tebl/C64-PlayOnTape/documentation/datasheets/805_connector.png

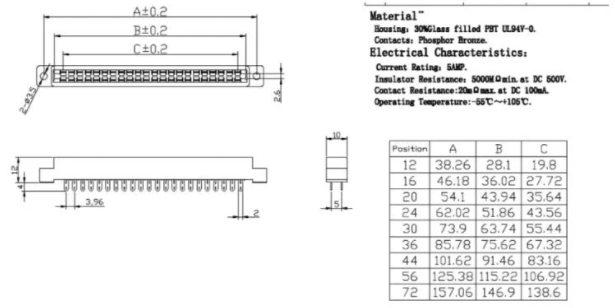
documentation/datasheets/805_connector.png
