tebl/C64-PlayOnTape/gallery/2022-02-19 01.37.31.jpg

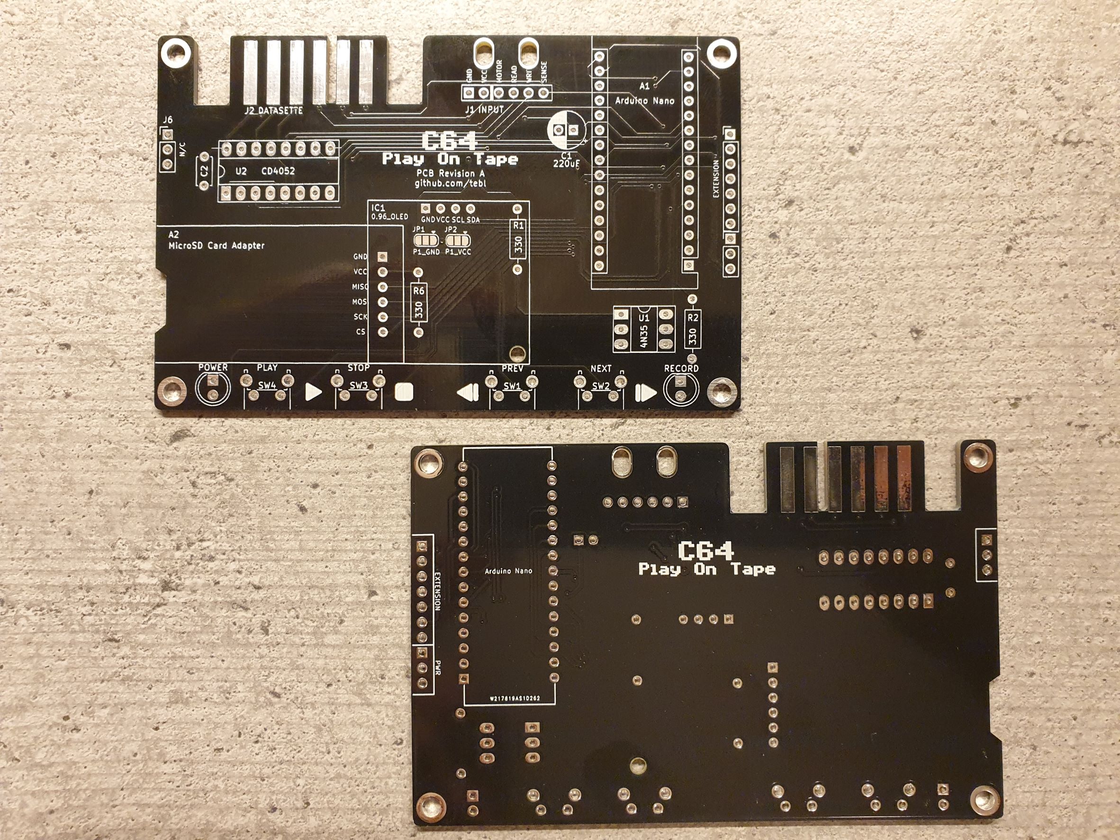
gallery/2022-02-19 01.37.31.jpg
