tebl/C64-PlayOnTape/gallery/2022-02-19 01.42.13.jpg

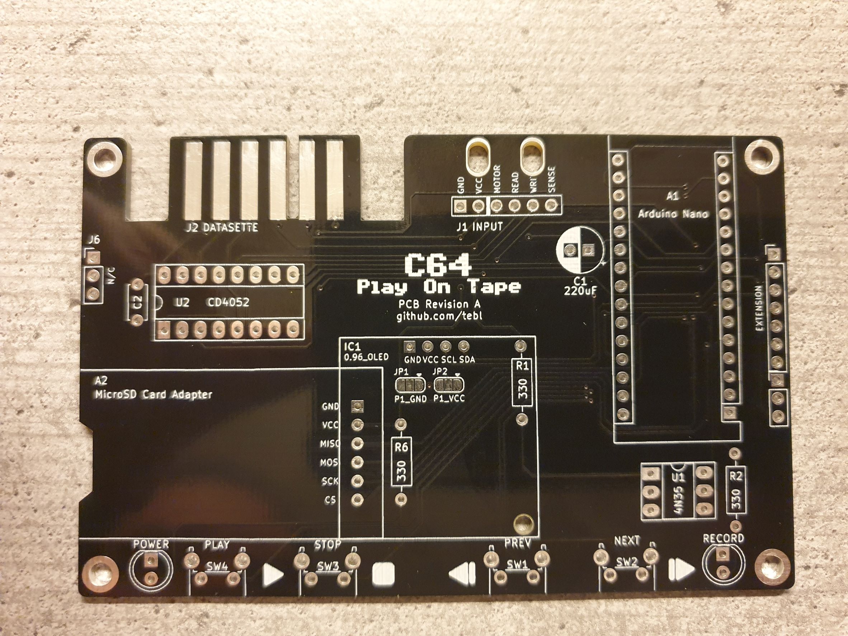
gallery/2022-02-19 01.42.13.jpg
