tebl/C64-PlayOnTape/gallery/2022-02-19 01.49.49.jpg

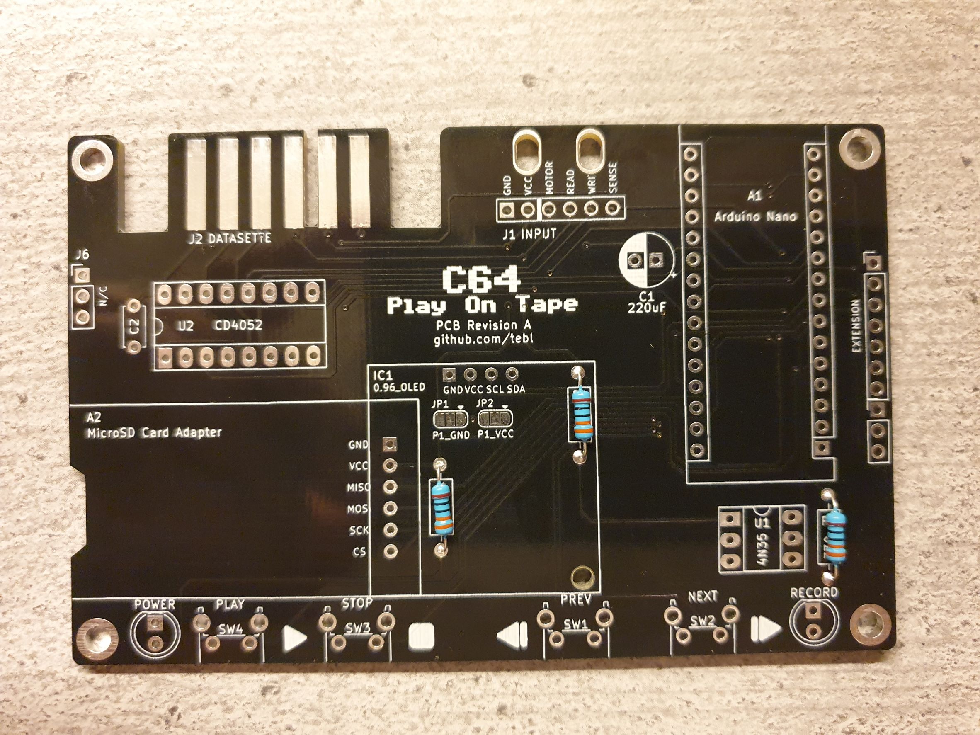
gallery/2022-02-19 01.49.49.jpg
