tebl/C64-PlayOnTape/gallery/2022-02-19 01.55.19.jpg

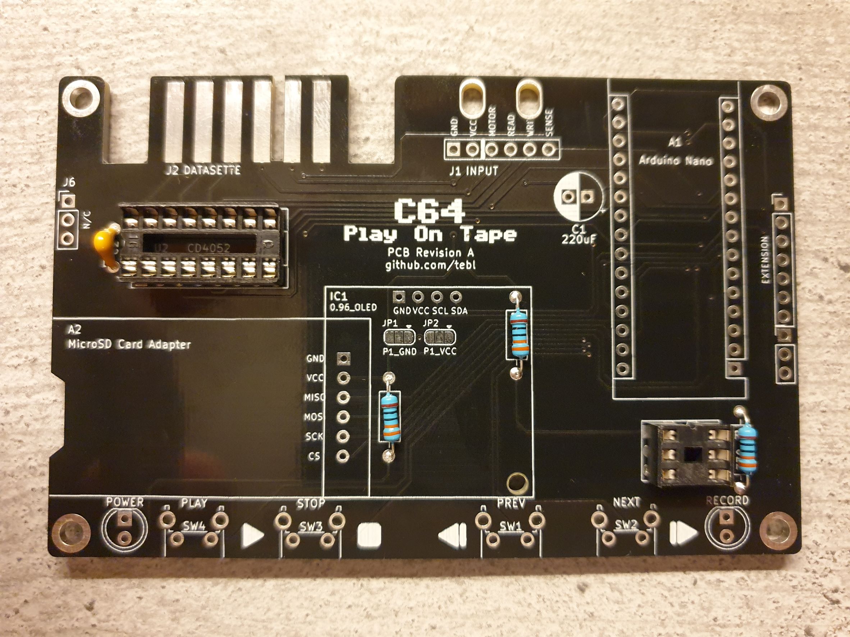
gallery/2022-02-19 01.55.19.jpg
