tebl/C64-PlayOnTape/gallery/2022-02-19 14.05.21.jpg

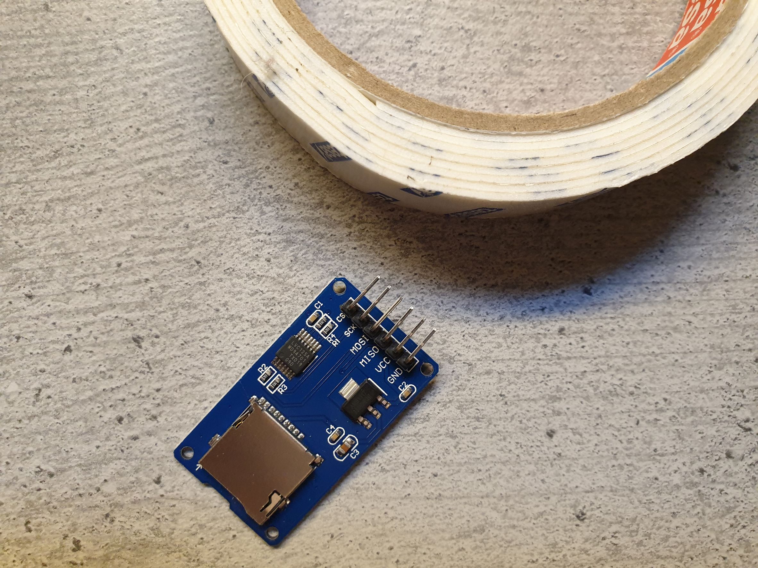
gallery/2022-02-19 14.05.21.jpg
