tebl/C64-PlayOnTape/gallery/2022-02-19 14.07.42.jpg

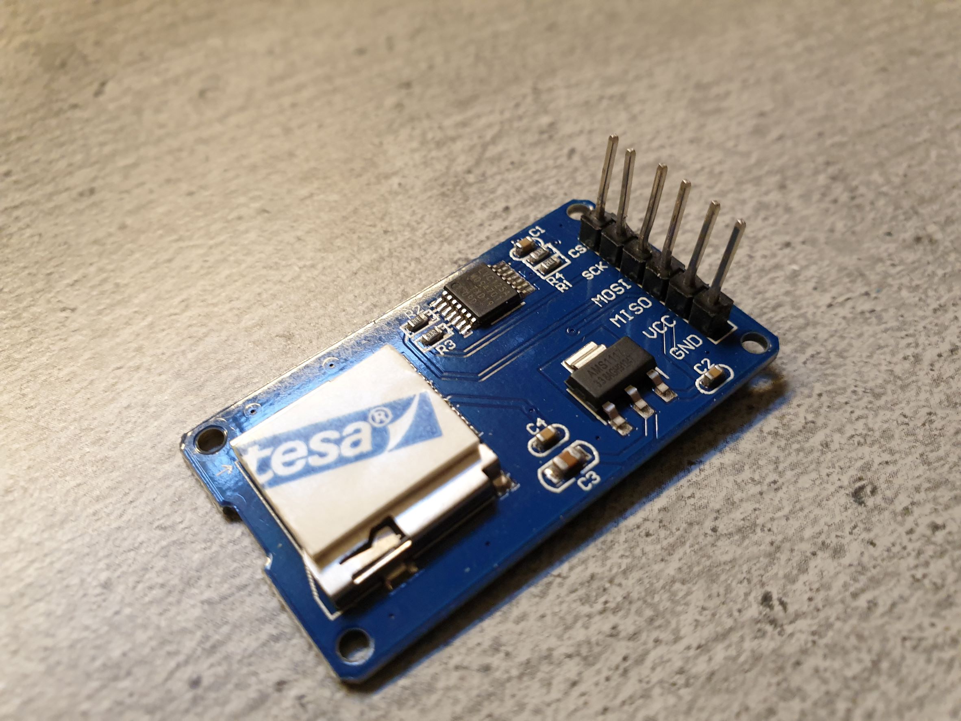
gallery/2022-02-19 14.07.42.jpg
