tebl/C64-PlayOnTape/gallery/2022-02-19 14.13.17.jpg

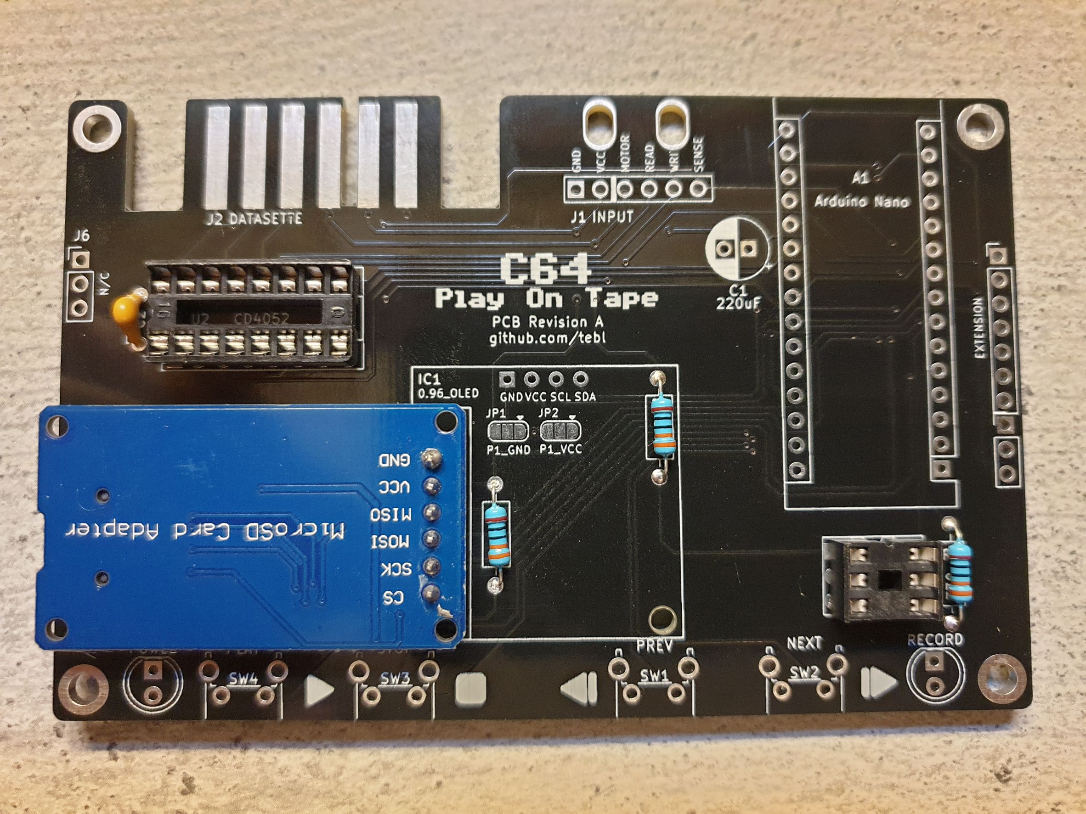
gallery/2022-02-19 14.13.17.jpg
