tebl/C64-PlayOnTape/gallery/2022-02-19 14.19.57.jpg

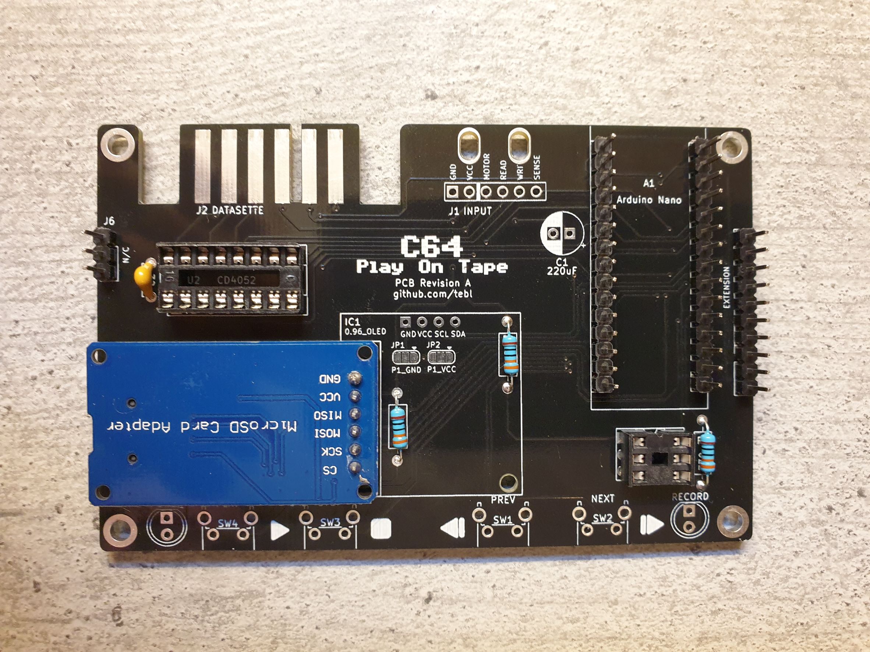
gallery/2022-02-19 14.19.57.jpg
