tebl/C64-PlayOnTape/gallery/2022-02-19 14.29.56.jpg

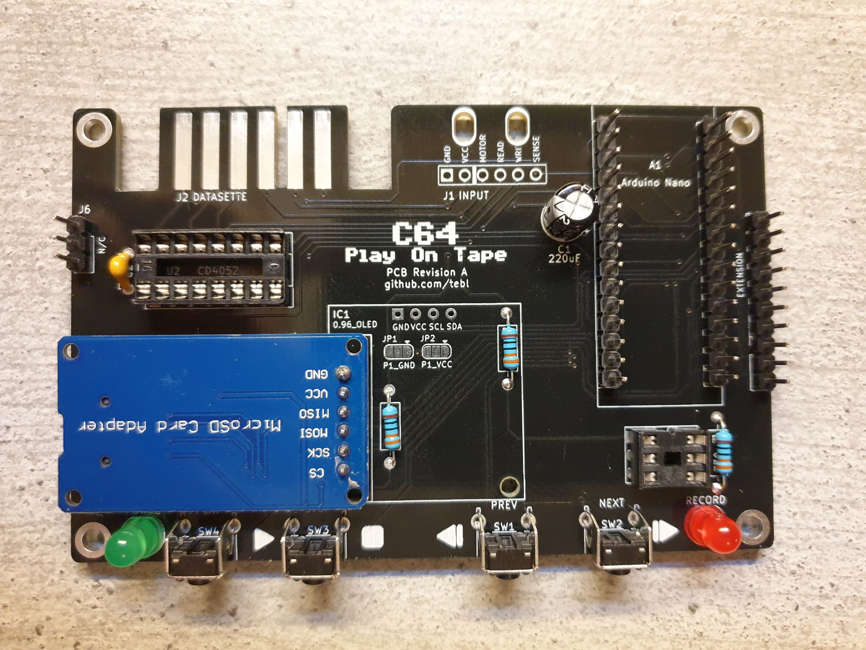
gallery/2022-02-19 14.29.56.jpg
