tebl/C64-PlayOnTape/gallery/2022-02-19 14.39.34.jpg

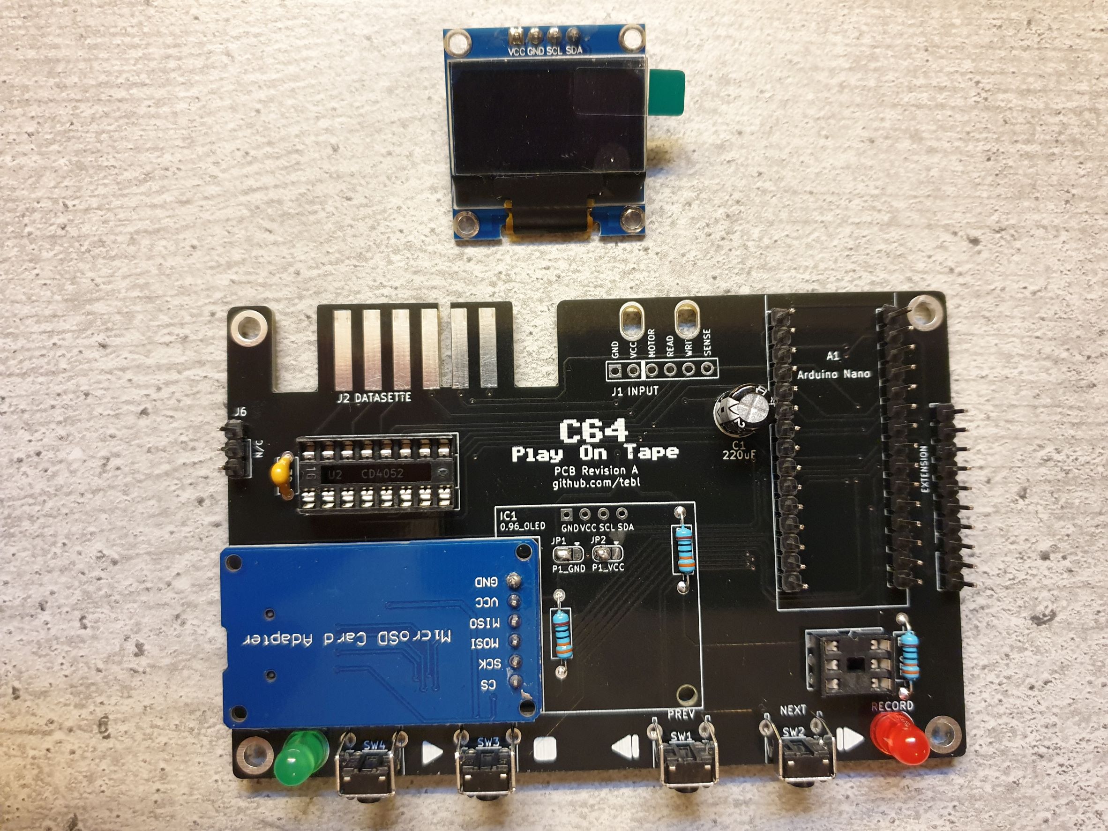
gallery/2022-02-19 14.39.34.jpg
