tebl/C64-PlayOnTape/gallery/2022-02-19 15.20.28.jpg

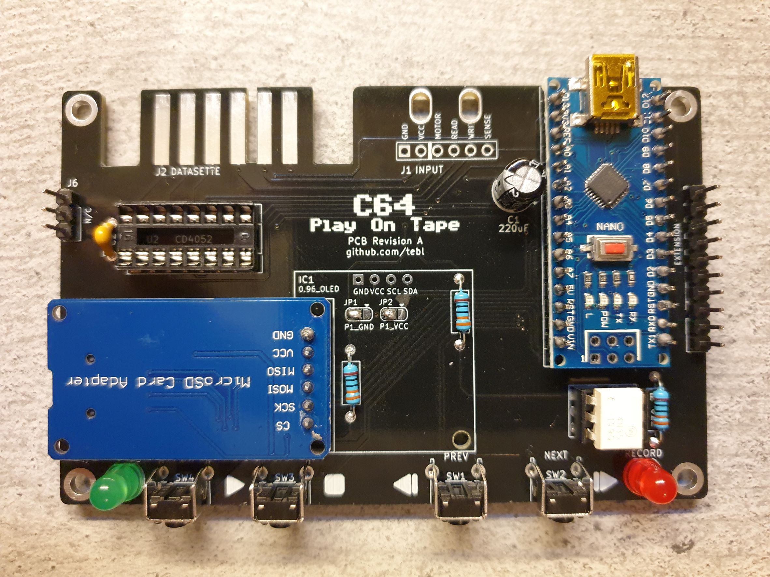
gallery/2022-02-19 15.20.28.jpg
