tebl/C64-PlayOnTape/gallery/2022-03-01 22.02.21.jpg

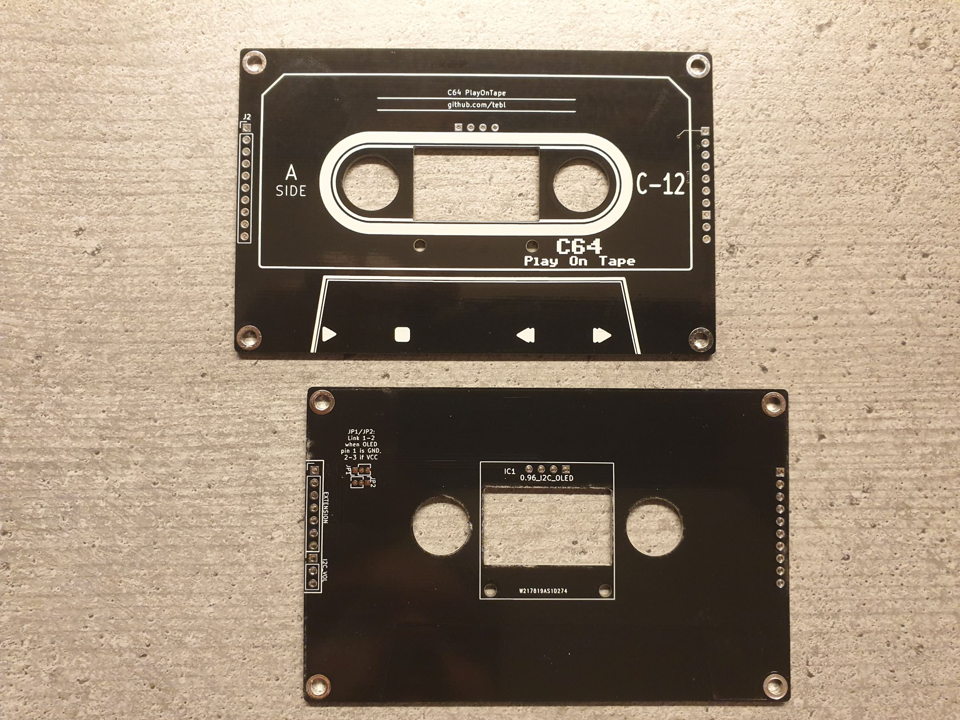
gallery/2022-03-01 22.02.21.jpg
