tebl/C64-PlayOnTape/gallery/2022-03-01 22.38.25.jpg

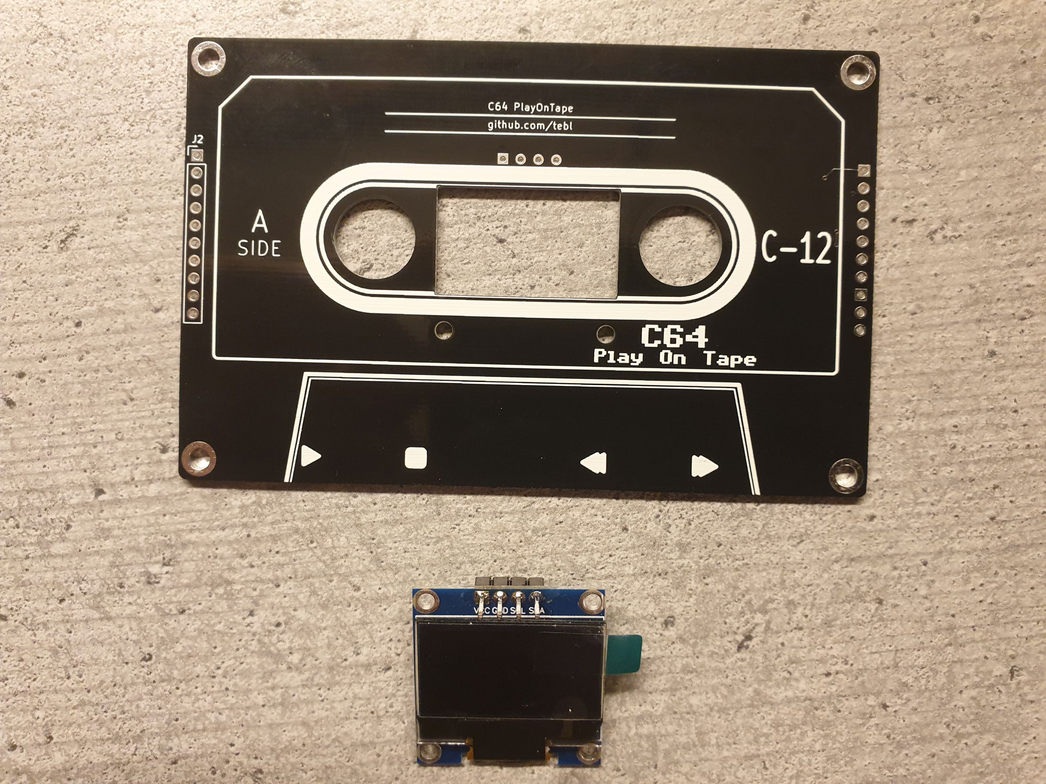
gallery/2022-03-01 22.38.25.jpg
