tebl/C64-PlayOnTape/gallery/2022-03-01 22.48.48.jpg

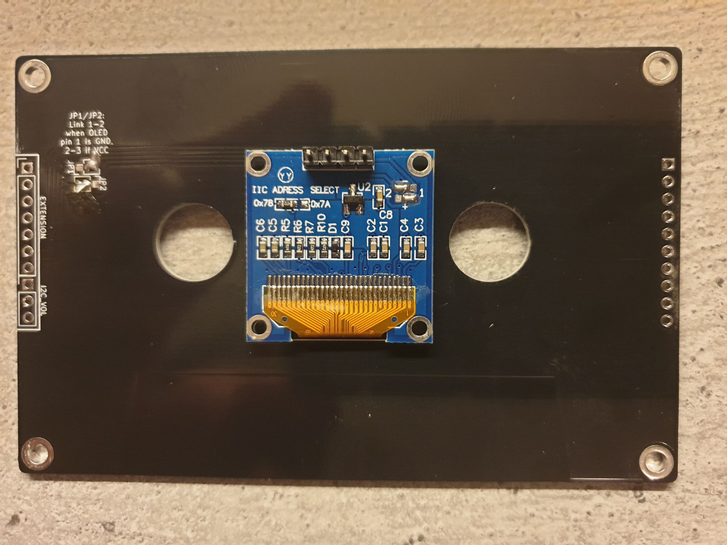
gallery/2022-03-01 22.48.48.jpg
