tebl/C64-PlayOnTape/gallery/2022-03-01 23.01.23.jpg

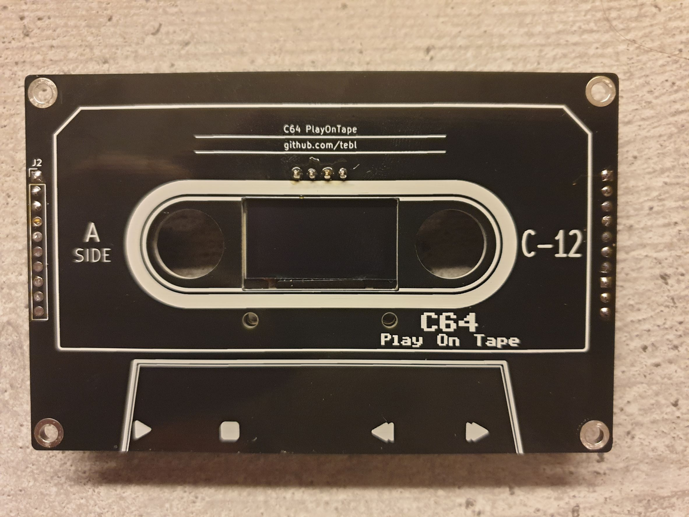
gallery/2022-03-01 23.01.23.jpg
