tebl/C64-PlayOnTape/gallery/2022-03-01 23.46.57.jpg

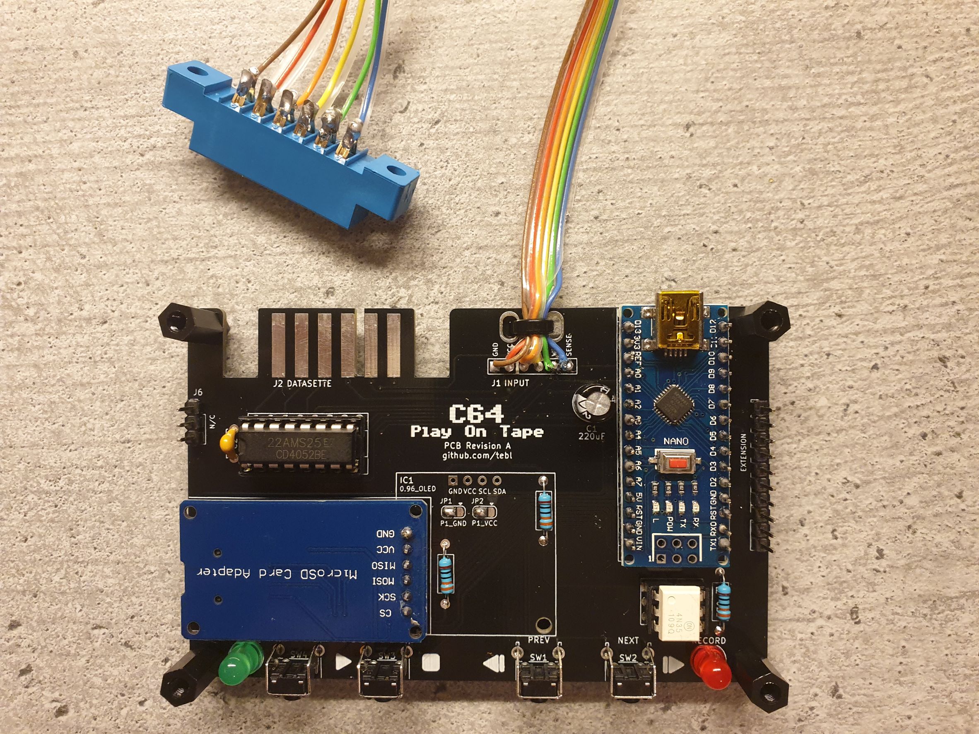
gallery/2022-03-01 23.46.57.jpg
