tebl/C64-PlayOnTape/gallery/2022-03-01 23.49.48.jpg

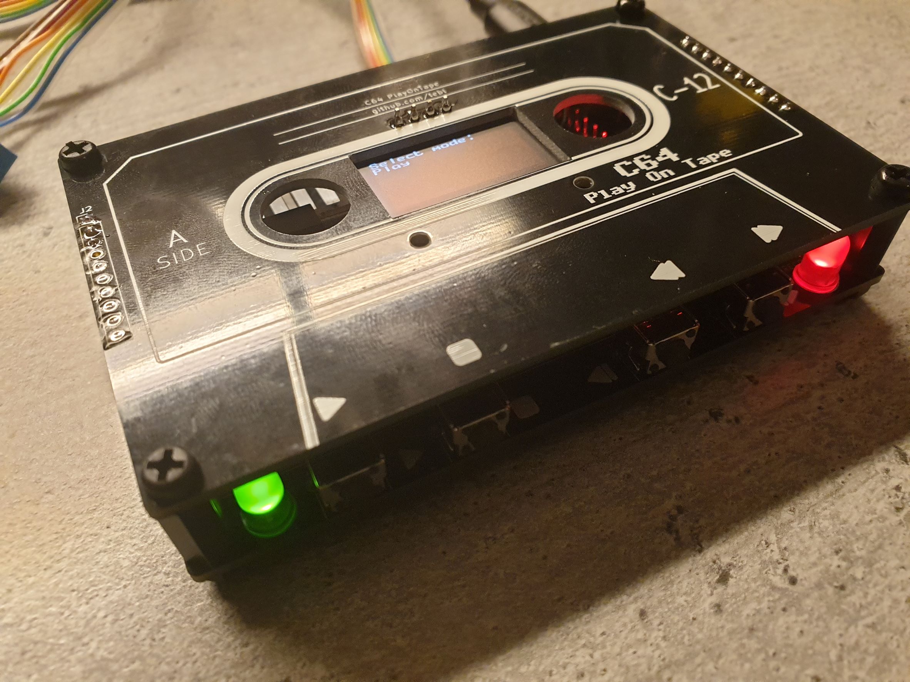
gallery/2022-03-01 23.49.48.jpg
