tebl/C64-PlayOnTape/gallery/2022-04-20 22.53.26.jpg

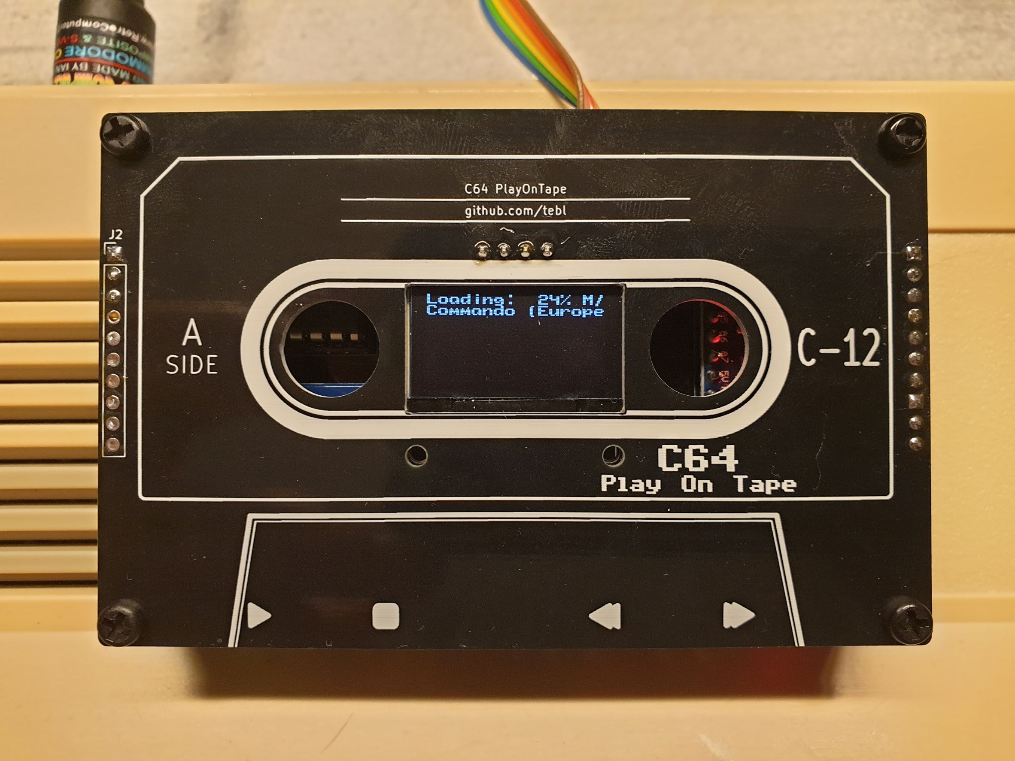
gallery/2022-04-20 22.53.26.jpg
