tebl/C64-PlayOnTape/gallery/2022-04-22 21.57.00.jpg

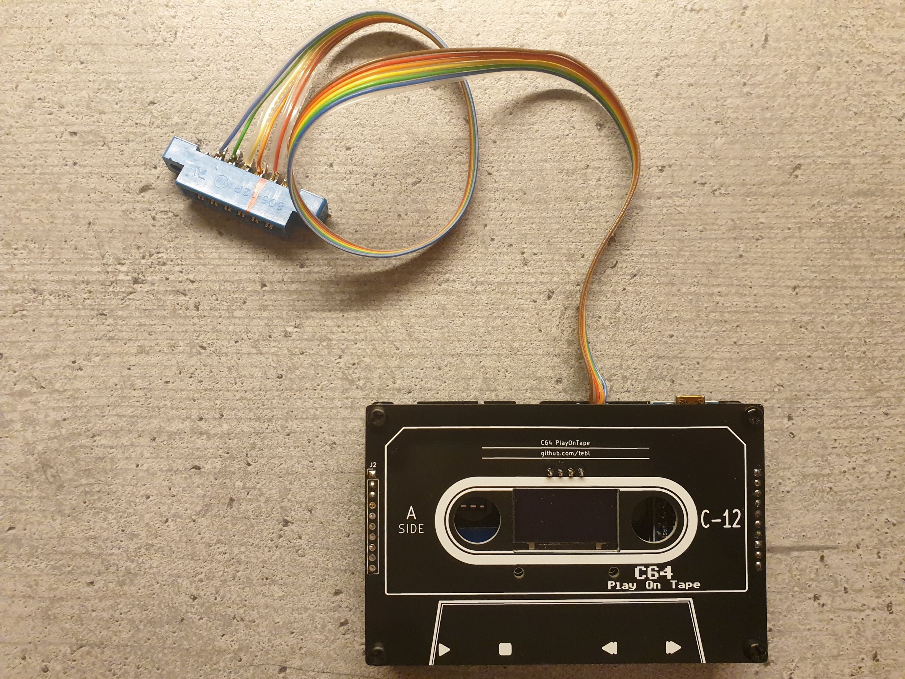
gallery/2022-04-22 21.57.00.jpg
