tebl/C64-PlayOnTape/gallery/2022-05-22 00.33.02.jpg

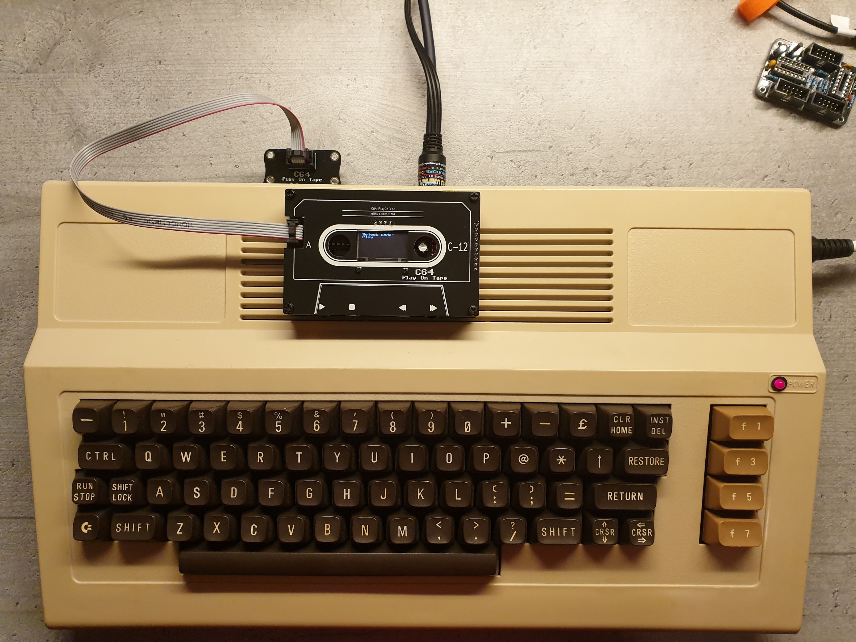
gallery/2022-05-22 00.33.02.jpg
