tebl/C64-PlayOnTape/gallery/2022-05-22 00.35.16.jpg

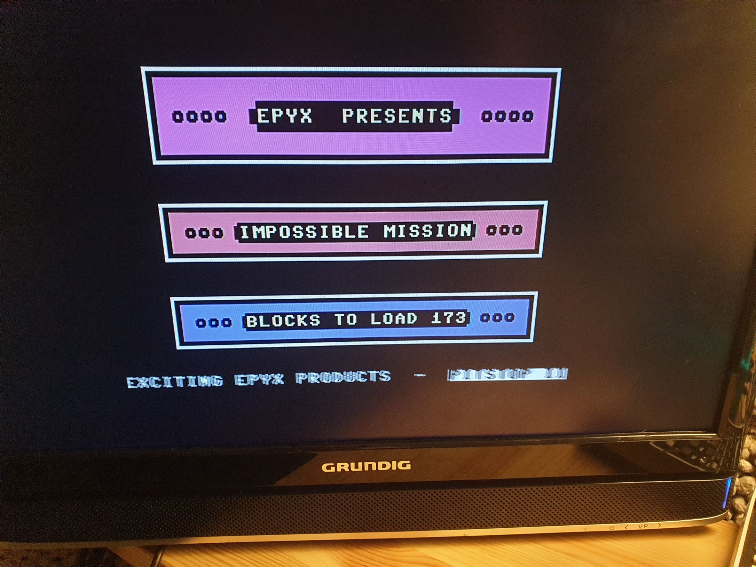
gallery/2022-05-22 00.35.16.jpg
