tebl/C64-PlayOnTape/gallery/2022-05-22 01.12.43.jpg

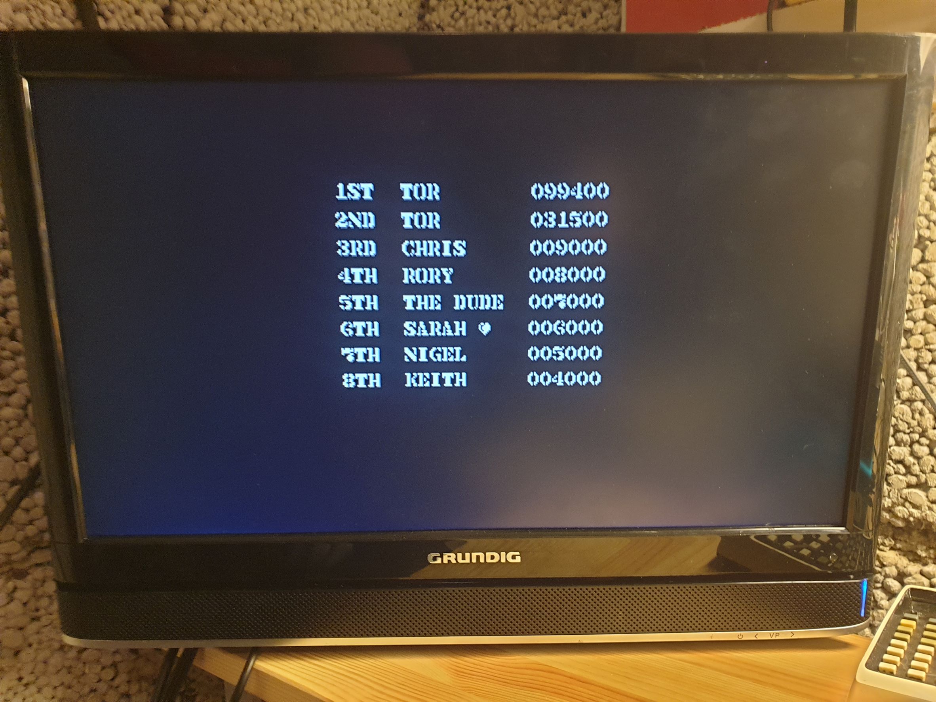
gallery/2022-05-22 01.12.43.jpg
