tebl/C64-PlayOnTape/gallery/PlayOnTape Backplate.png

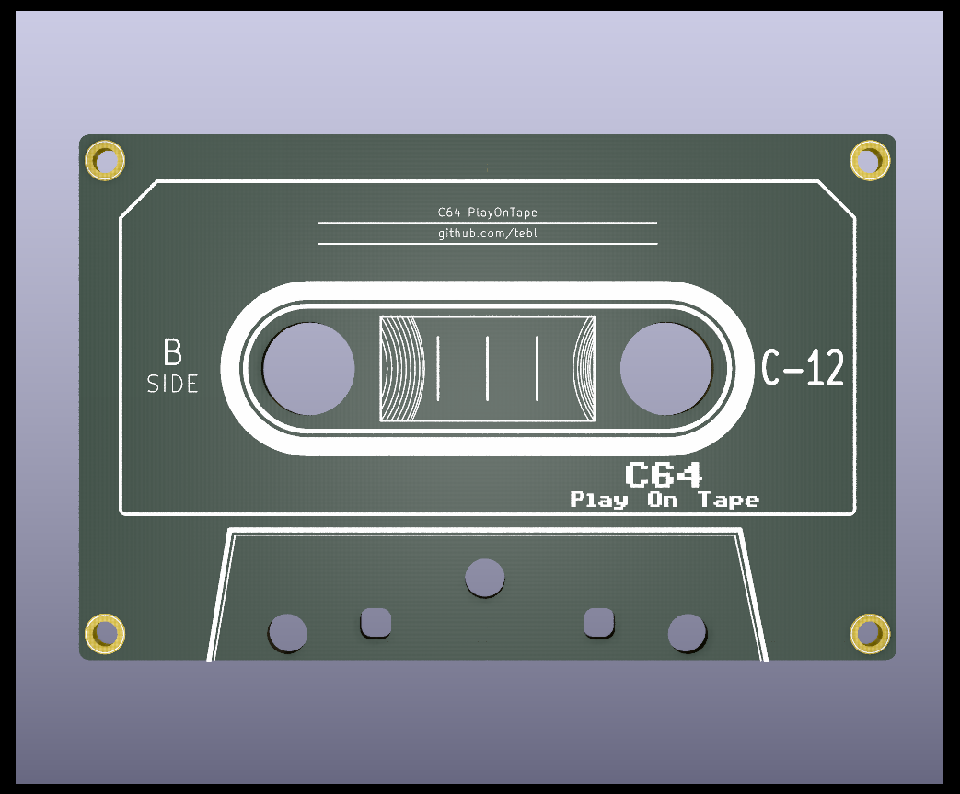
gallery/PlayOnTape Backplate.png
