tebl/C64-PlayOnTape/gallery/PlayOnTape Faceplate A1.png

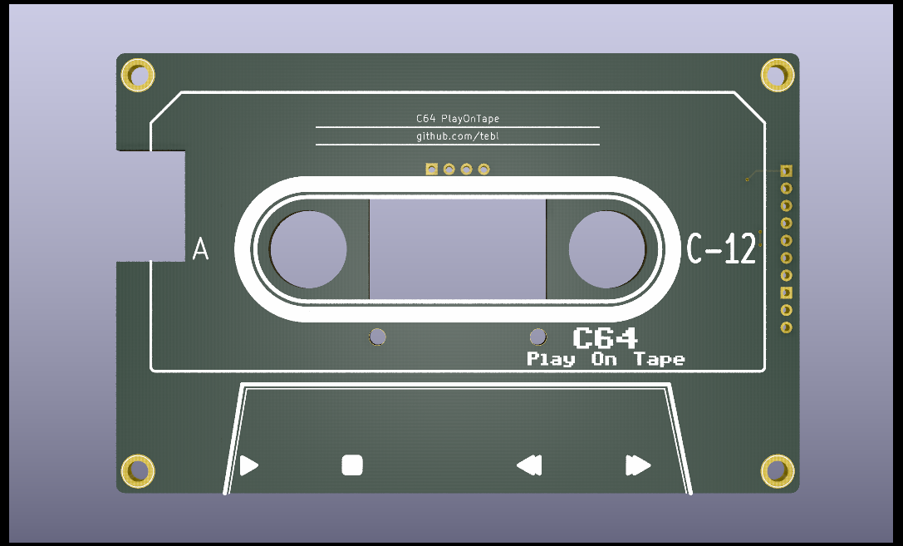
gallery/PlayOnTape Faceplate A1.png
