tebl/C64-PlayOnTape/gallery/PlayOnTape Module.png

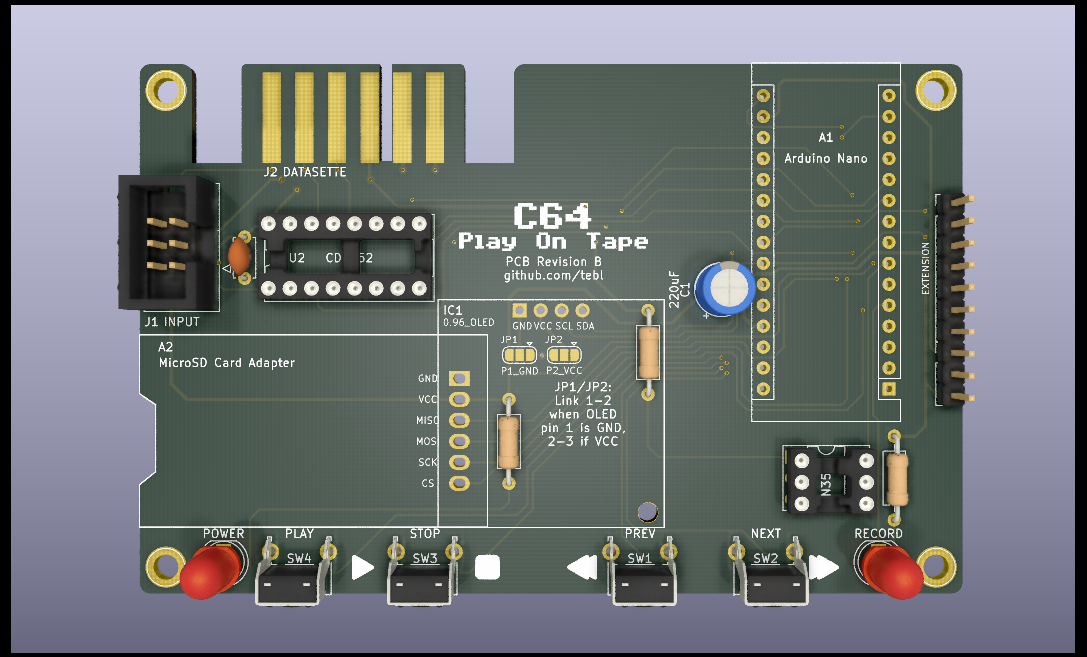
gallery/PlayOnTape Module.png
