tebl/C64-PlayOnTape/gallery/build_module_009.jpg

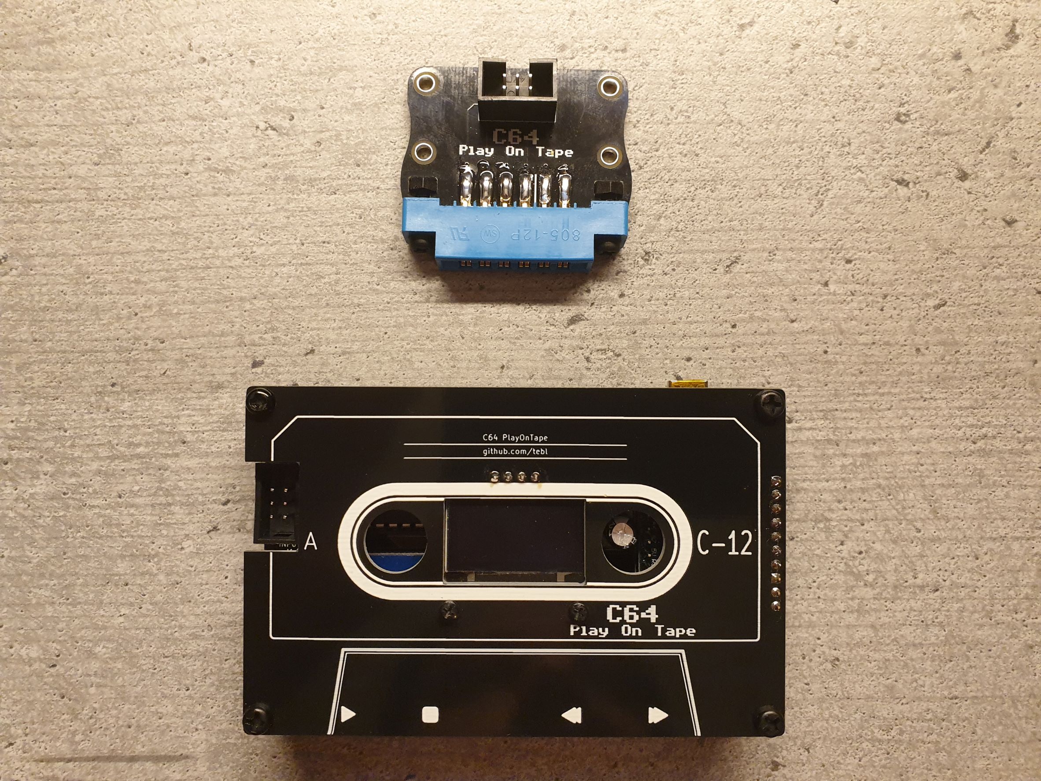
gallery/build_module_009.jpg
