tebl/C64-PlayOnTape/gallery/build_module_010.jpg

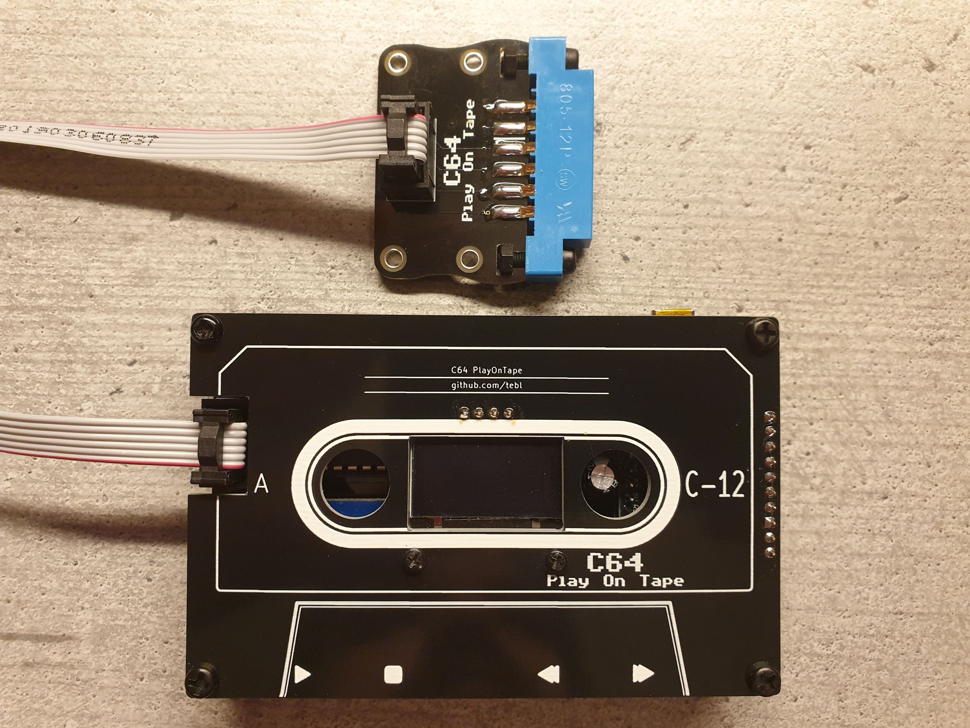
gallery/build_module_010.jpg
